martinkadauke/intercom/hardware/parts/agro-595-15-as.png

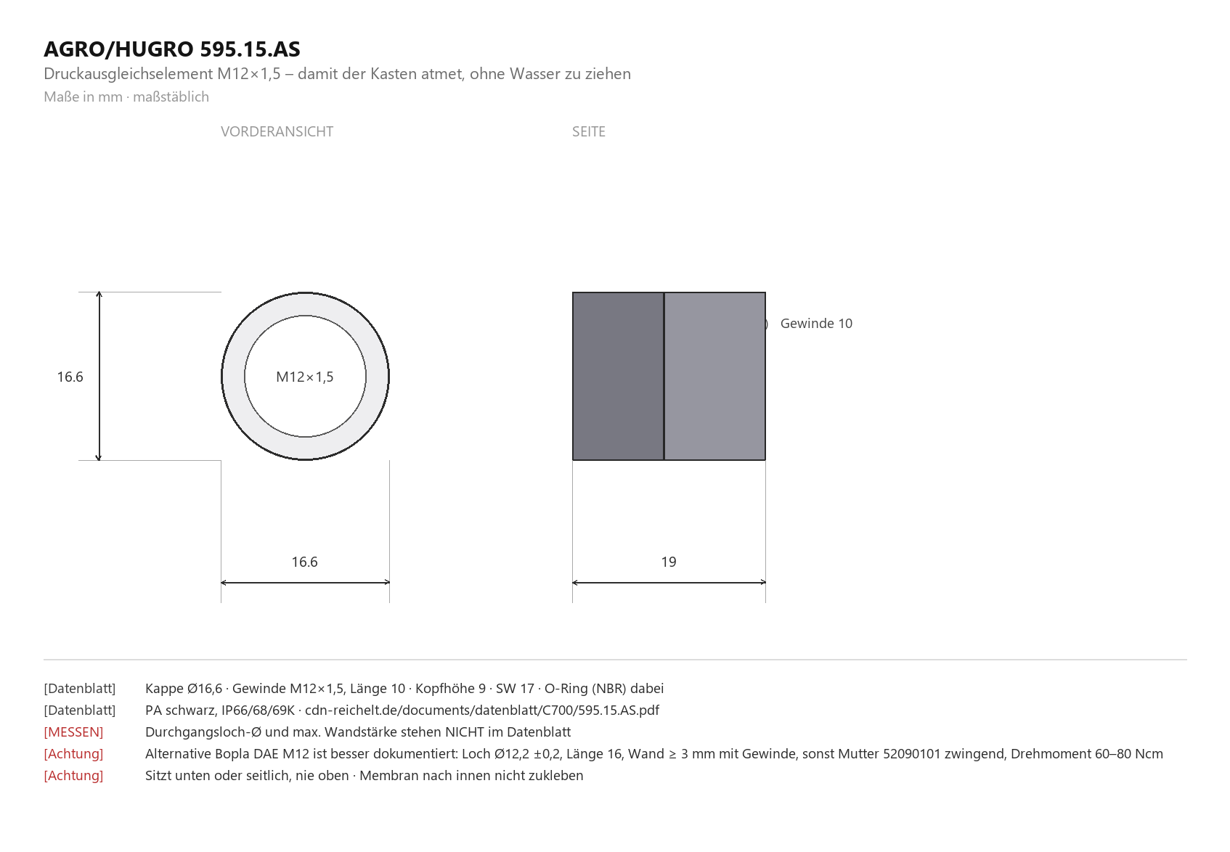
hardware/parts/agro-595-15-as.png
