martinkadauke/intercom/hardware/parts/bme280.png

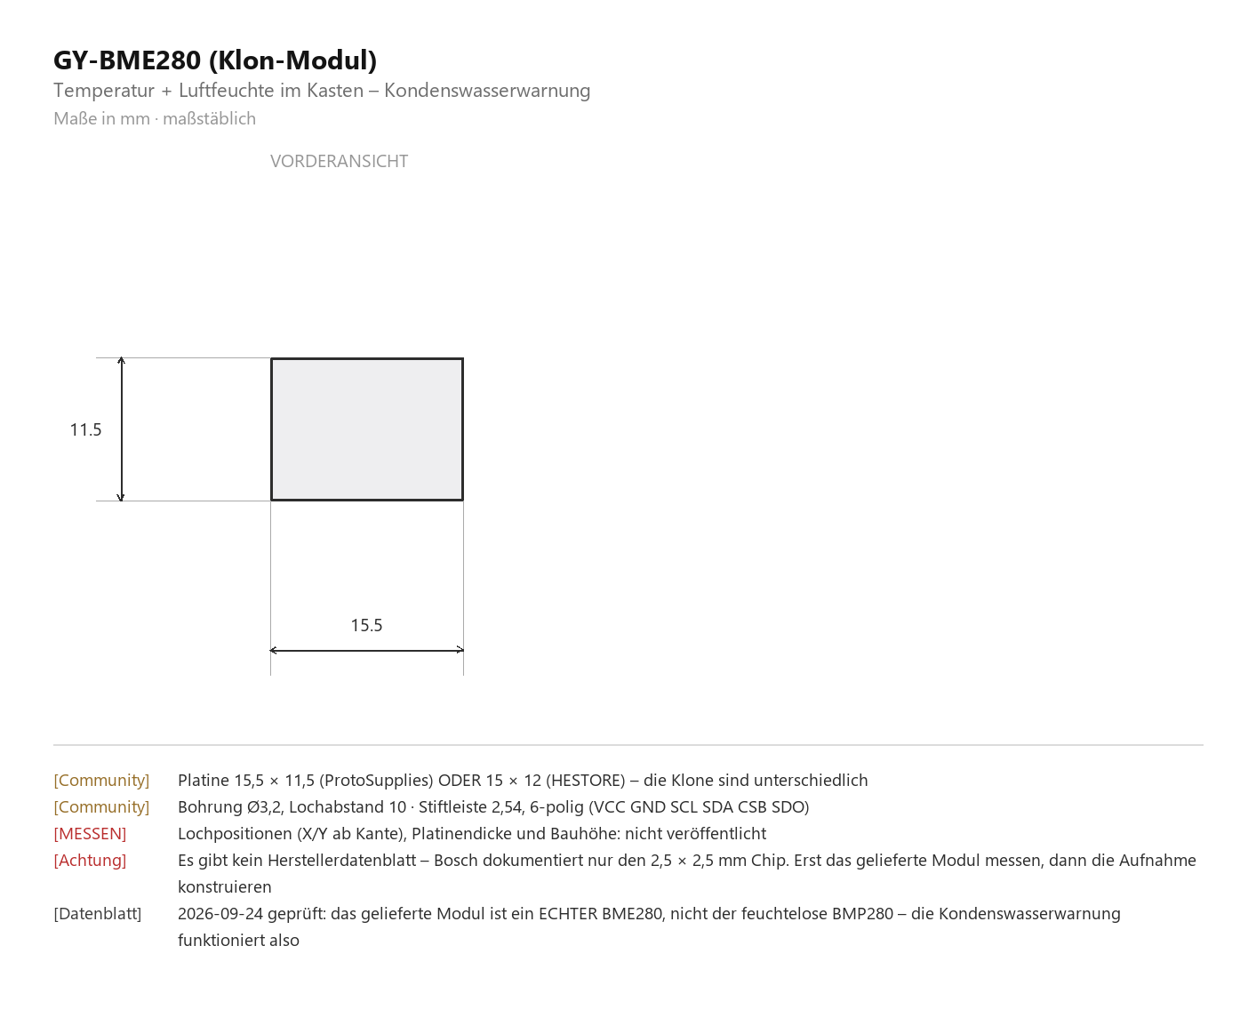
hardware/parts/bme280.png
