martinkadauke/intercom/hardware/parts/heizpad.png

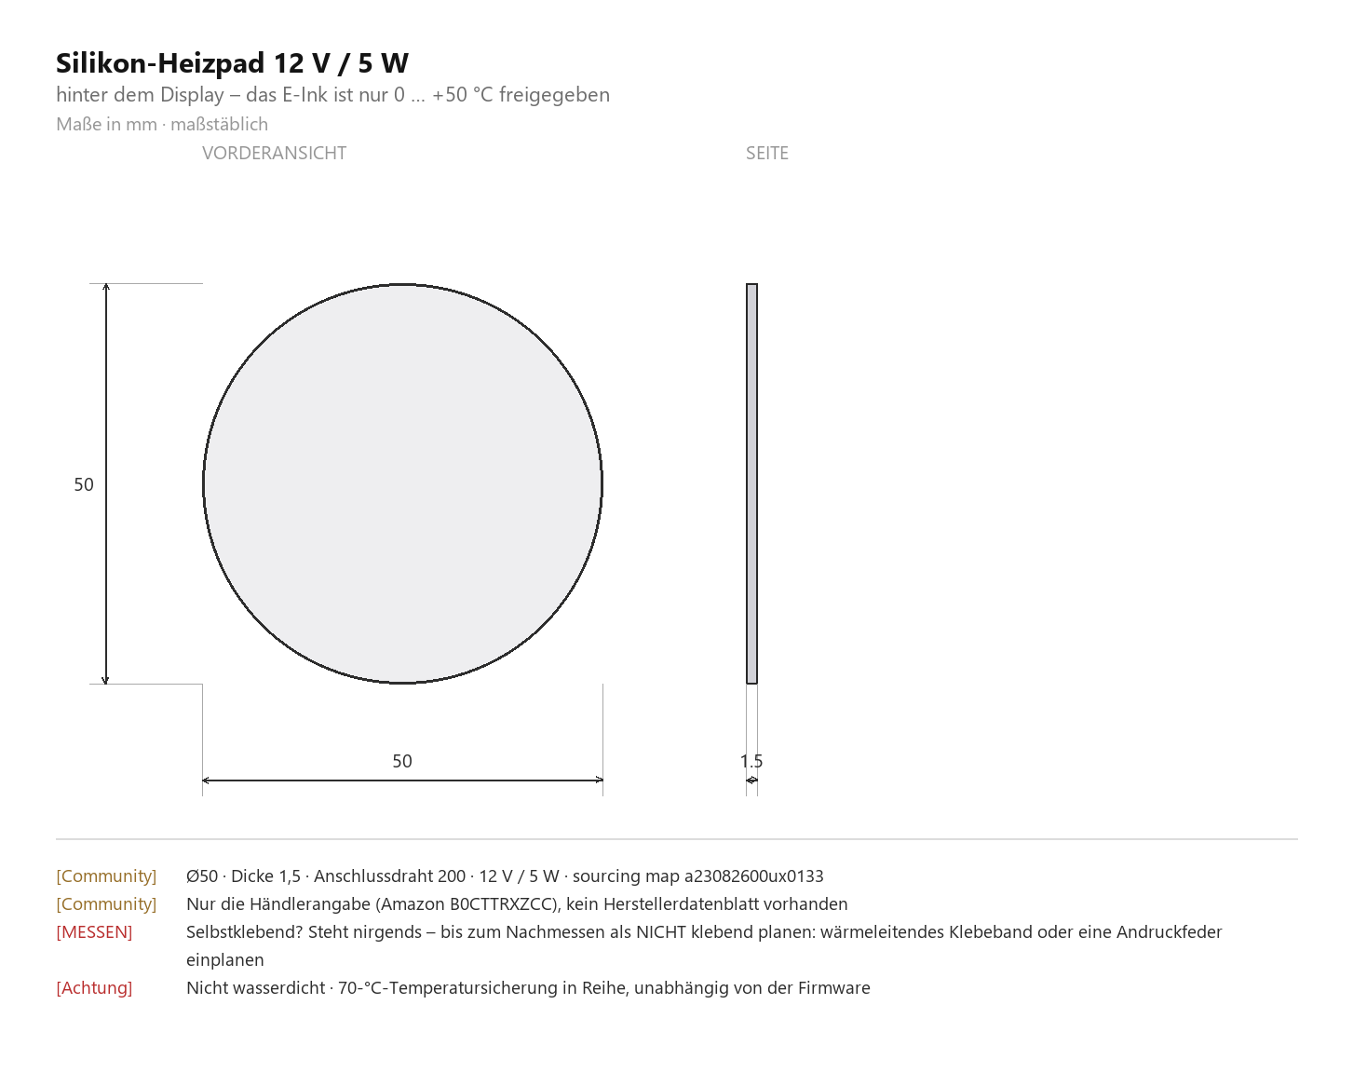
hardware/parts/heizpad.png
