martinkadauke/intercom/hardware/parts/lautsprecher-k40sq.png

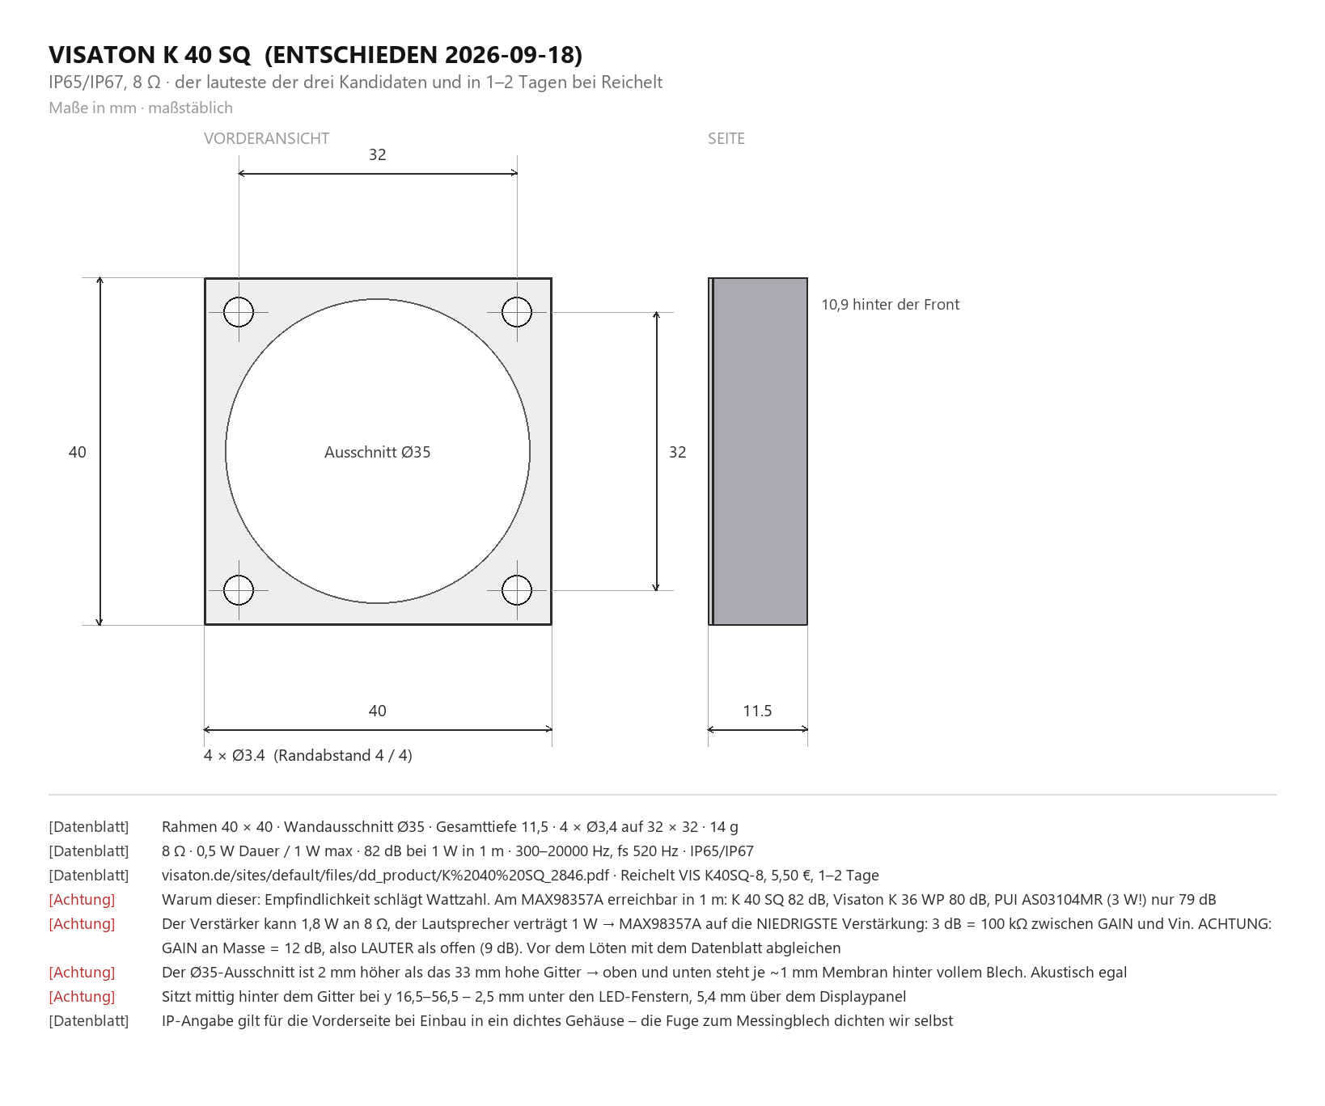
hardware/parts/lautsprecher-k40sq.png
