martinkadauke/intercom/hardware/parts/max98357a.png

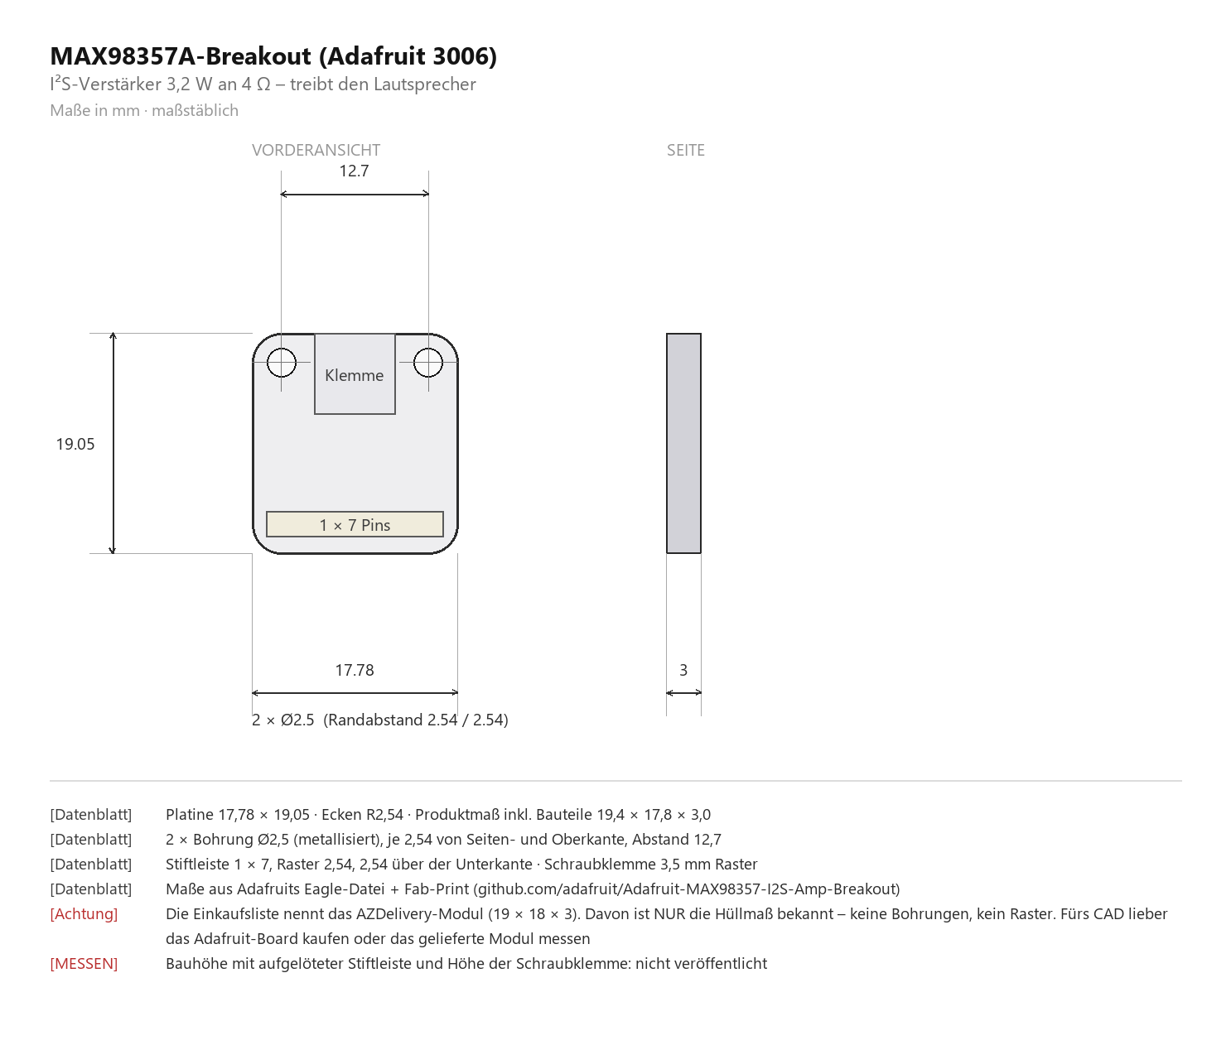
hardware/parts/max98357a.png
