martinkadauke/intercom/hardware/parts/pololu-d30v30f5.png

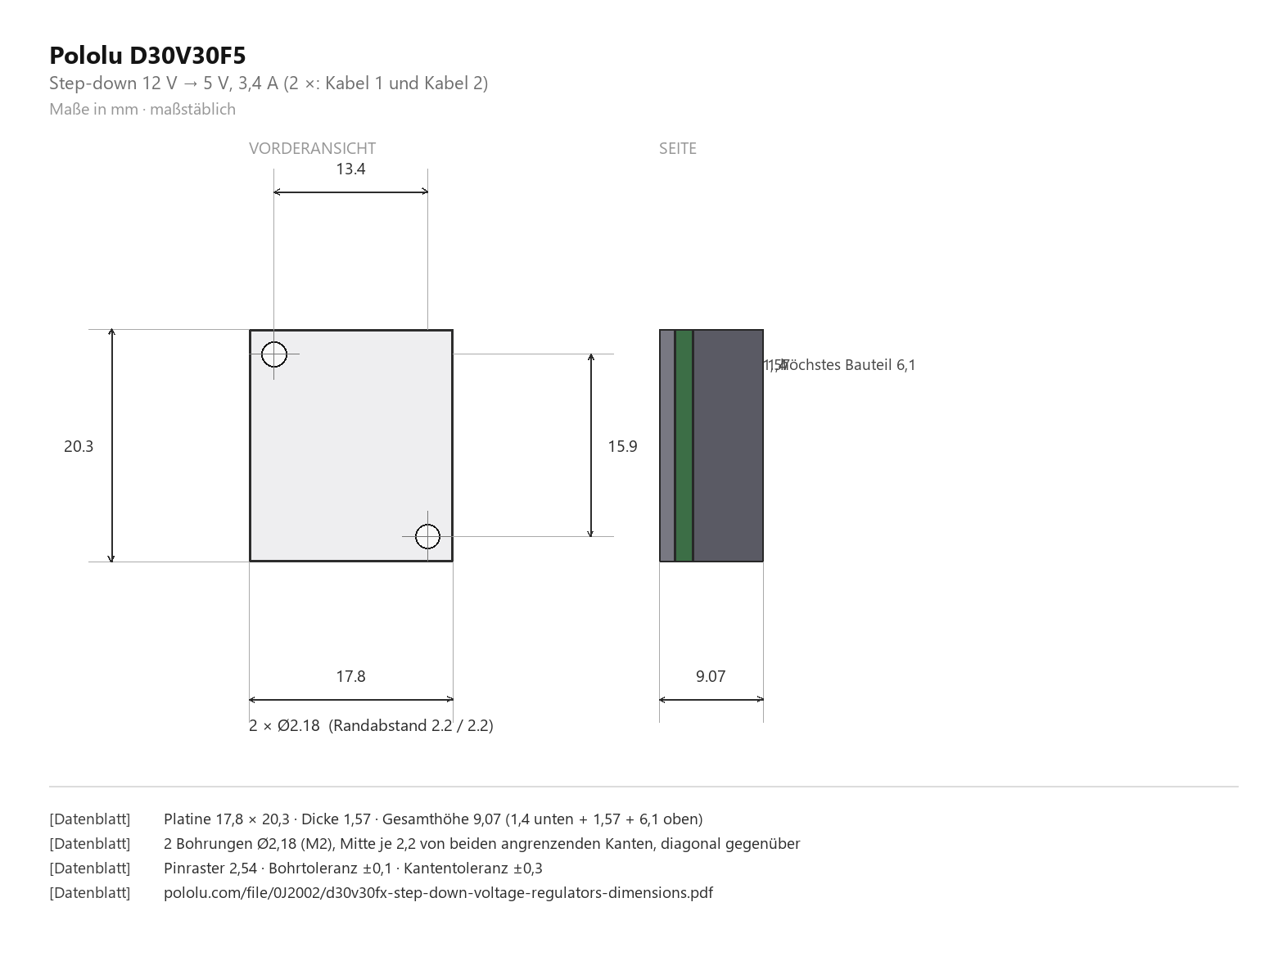
hardware/parts/pololu-d30v30f5.png
