martinkadauke/intercom/hardware/parts/sk6812.png

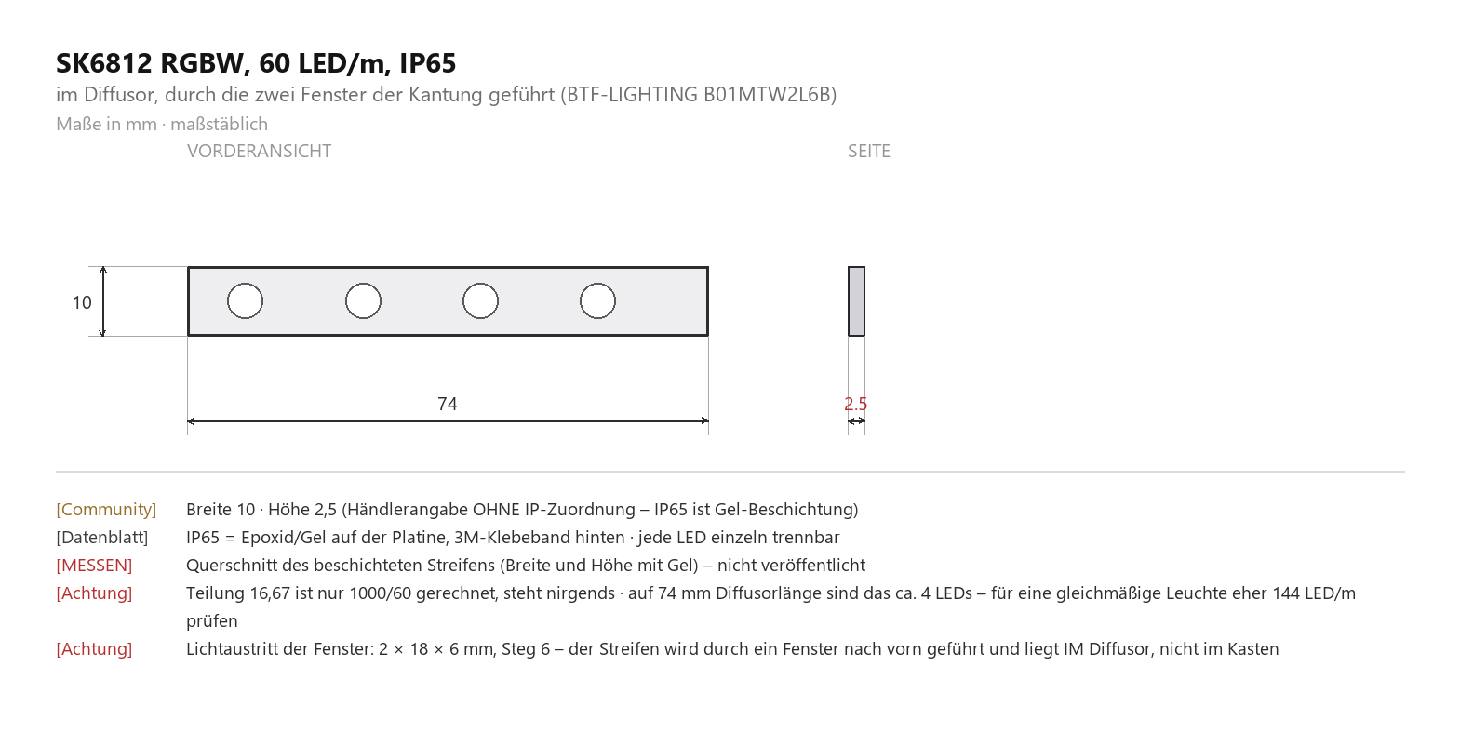
hardware/parts/sk6812.png
