martinkadauke/intercom/hardware/parts/waveshare-s3-eth.png

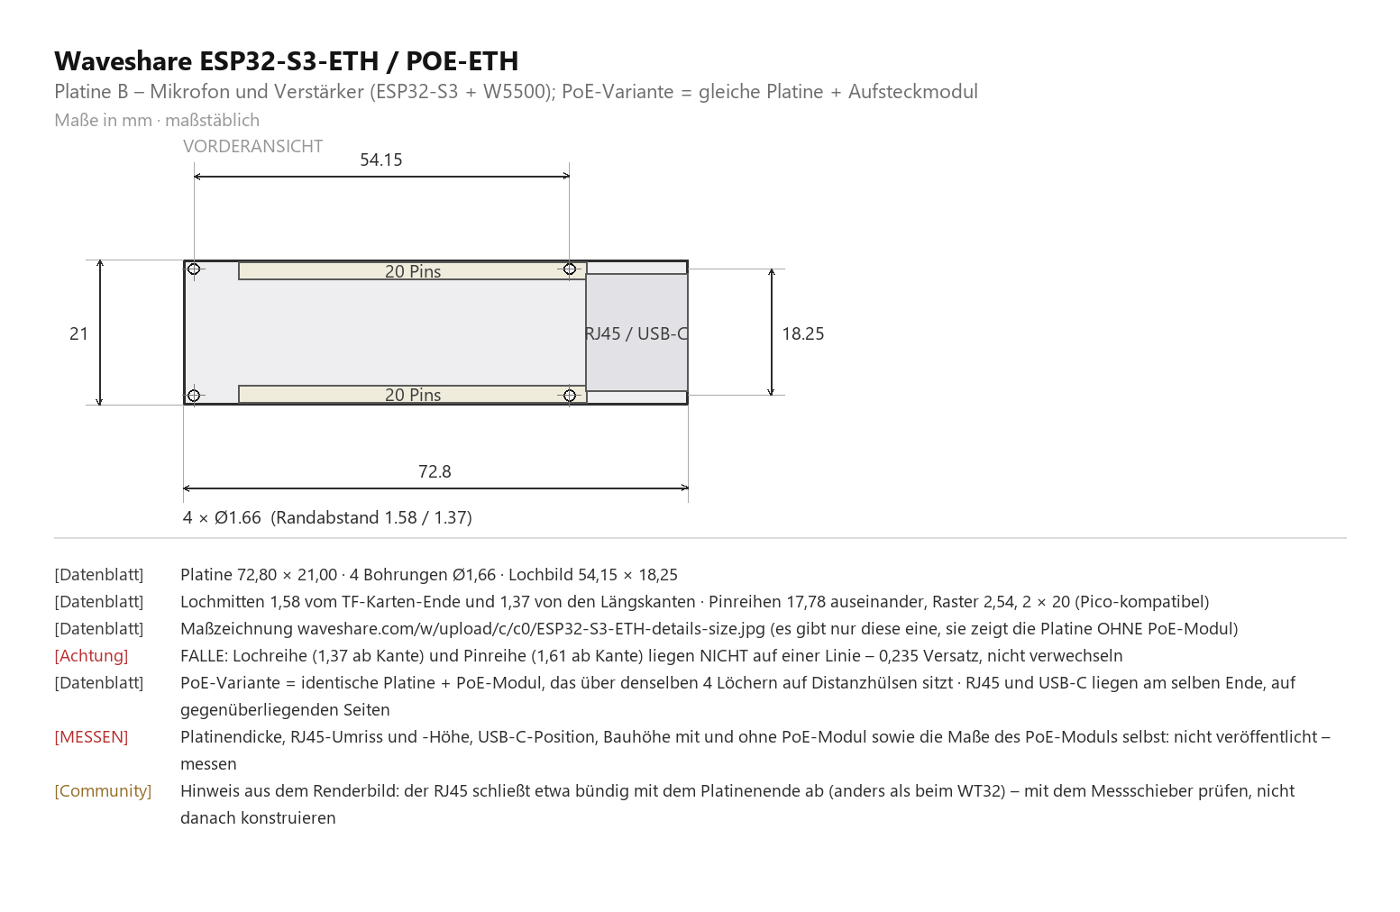
hardware/parts/waveshare-s3-eth.png
