martinkadauke/intercom/hardware/parts/wt32-eth01.png

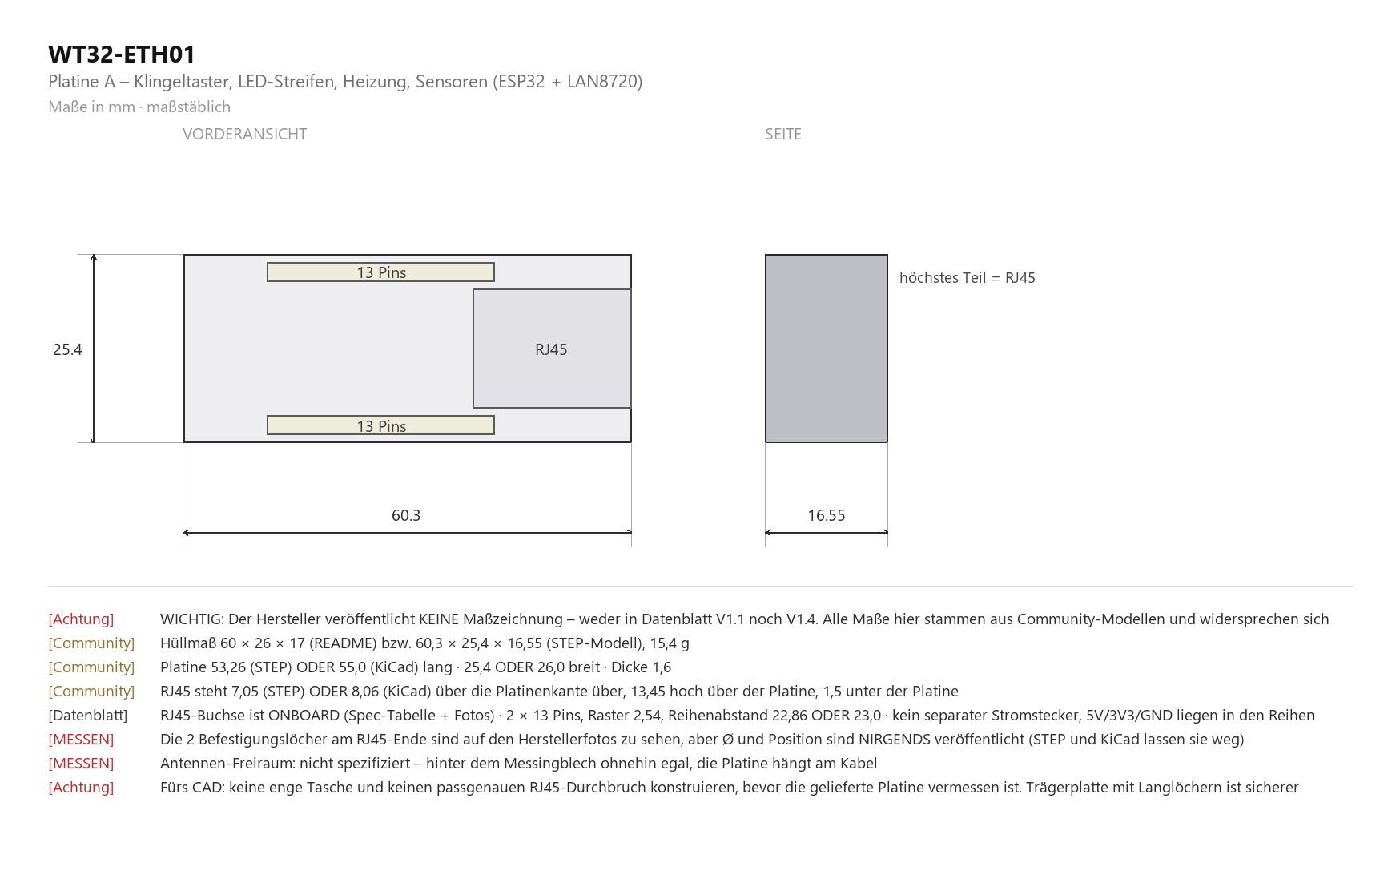
hardware/parts/wt32-eth01.png
